elseby/SebyDBtnX/hardware/SebyDBtn4/pcb/4.0/PNG_Schematic_1_2025-09-06/SCH_Schematic_1_1-HIBus Interface - Power_2025-09-06.png

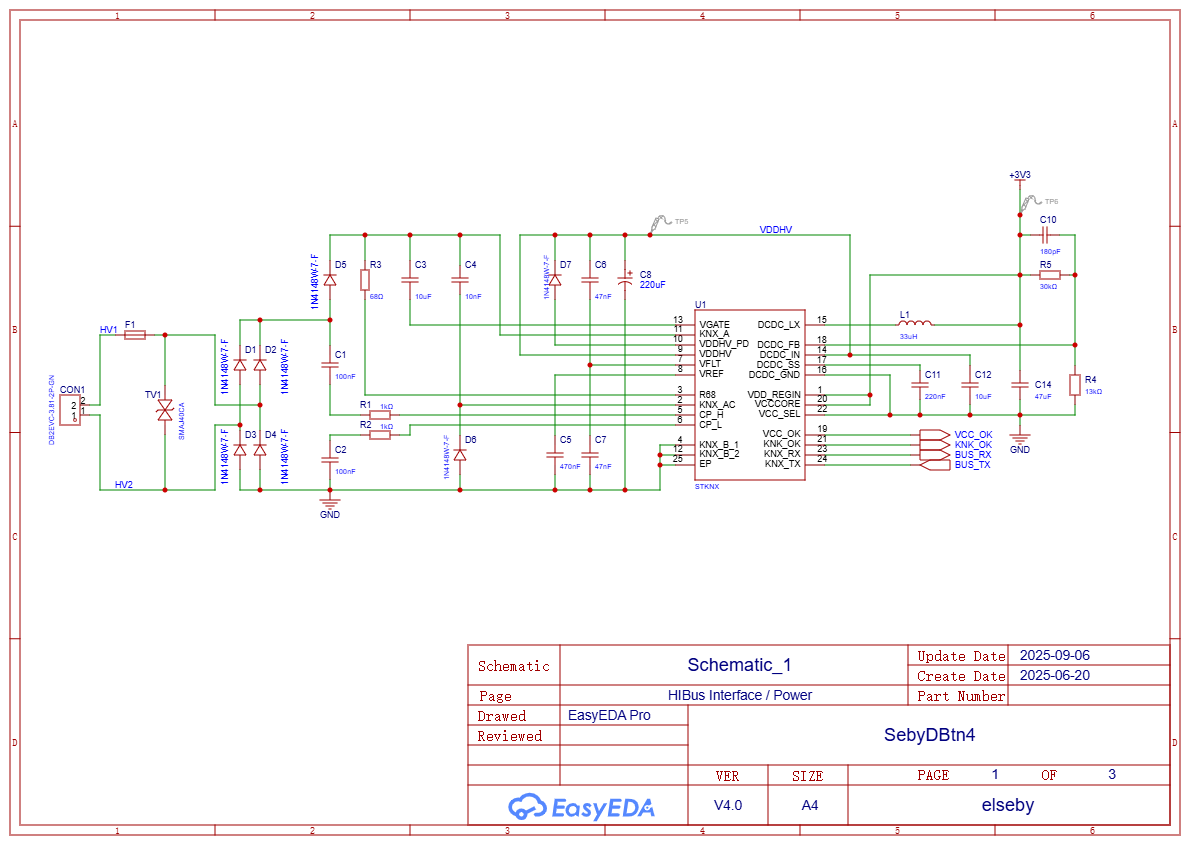
hardware/SebyDBtn4/pcb/4.0/PNG_Schematic_1_2025-09-06/SCH_Schematic_1_1-HIBus Interface - Power_2025-09-06.png
