elseby/SebyDBtnX/images/3D_SebyDBtn8_PCB_3.0_back.png

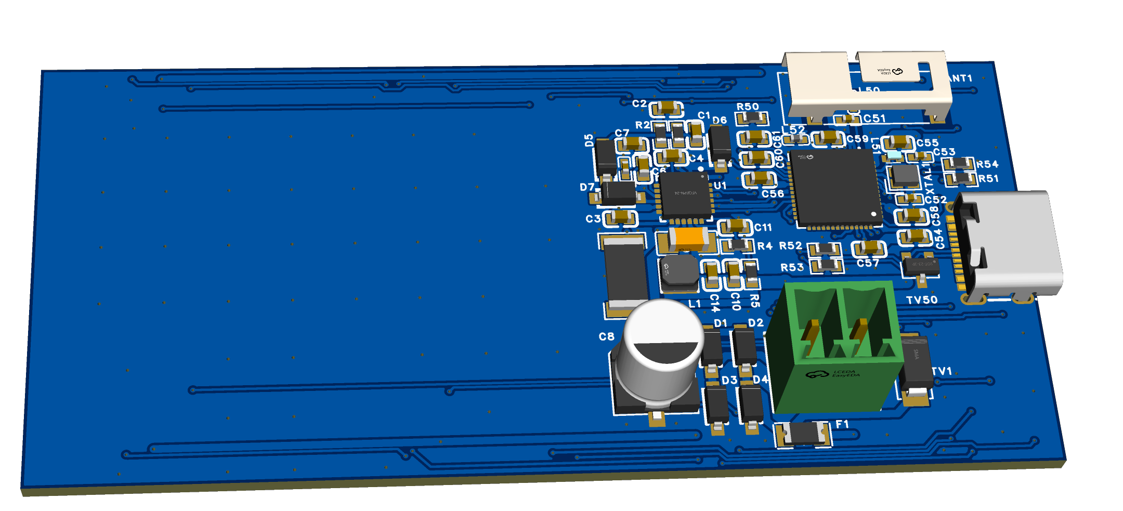
images/3D_SebyDBtn8_PCB_3.0_back.png
