elseby/SebyDBtnX/images/3D_SebyDBtn8_PCB_3.0_front.png

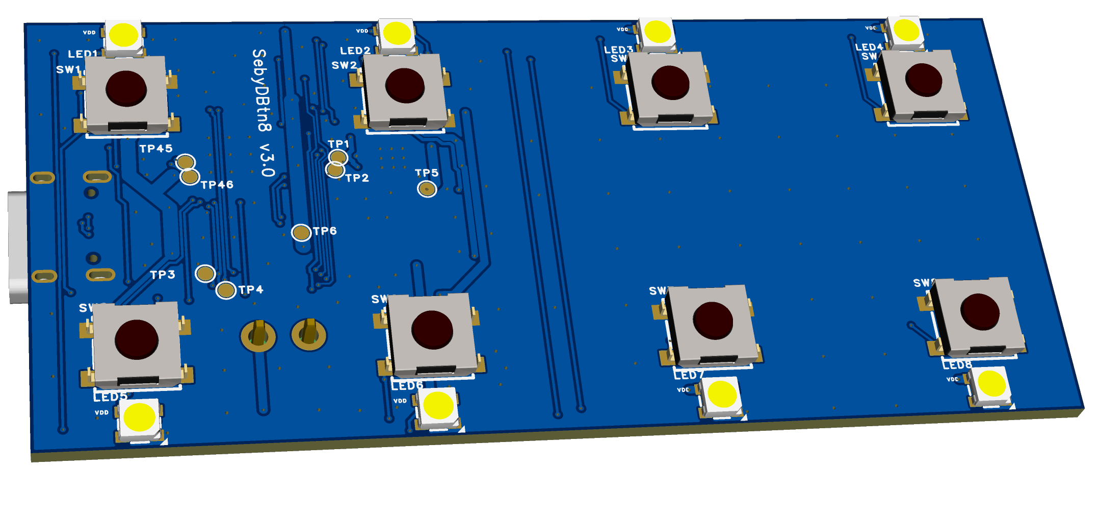
images/3D_SebyDBtn8_PCB_3.0_front.png
