elseby/SebyDBtnX/images/SebyDBtn4_coverfront.png

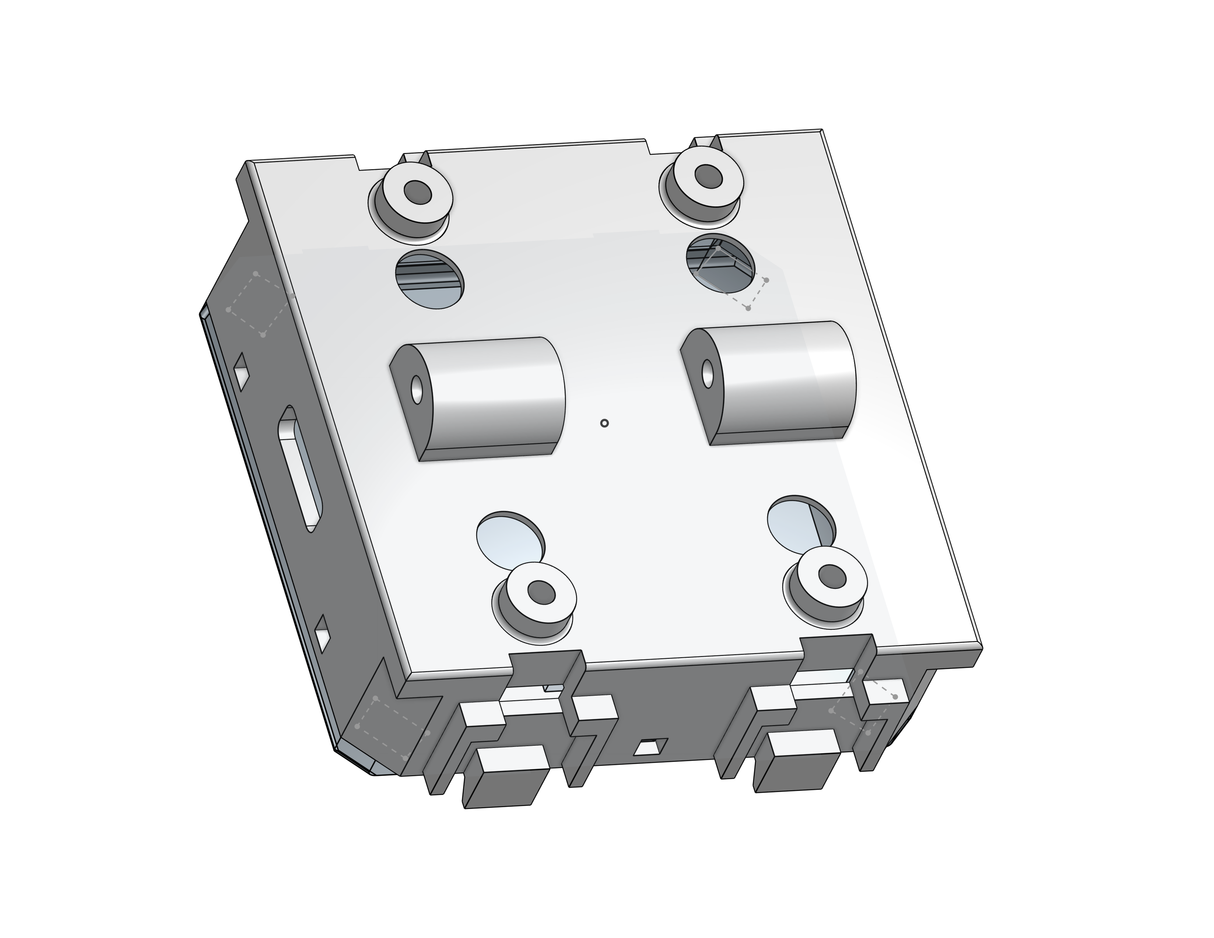
images/SebyDBtn4_coverfront.png
