elseby/SebyDBtnX/images/SebyDBtn8_BackCover_V3.0.png

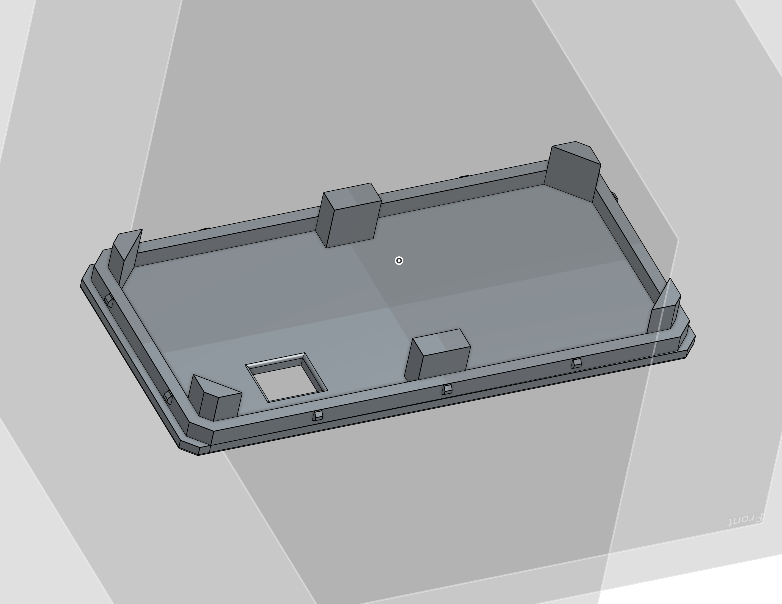
images/SebyDBtn8_BackCover_V3.0.png
