elseby/SebyDBtnX/images/SebyDBtn8_cover.png

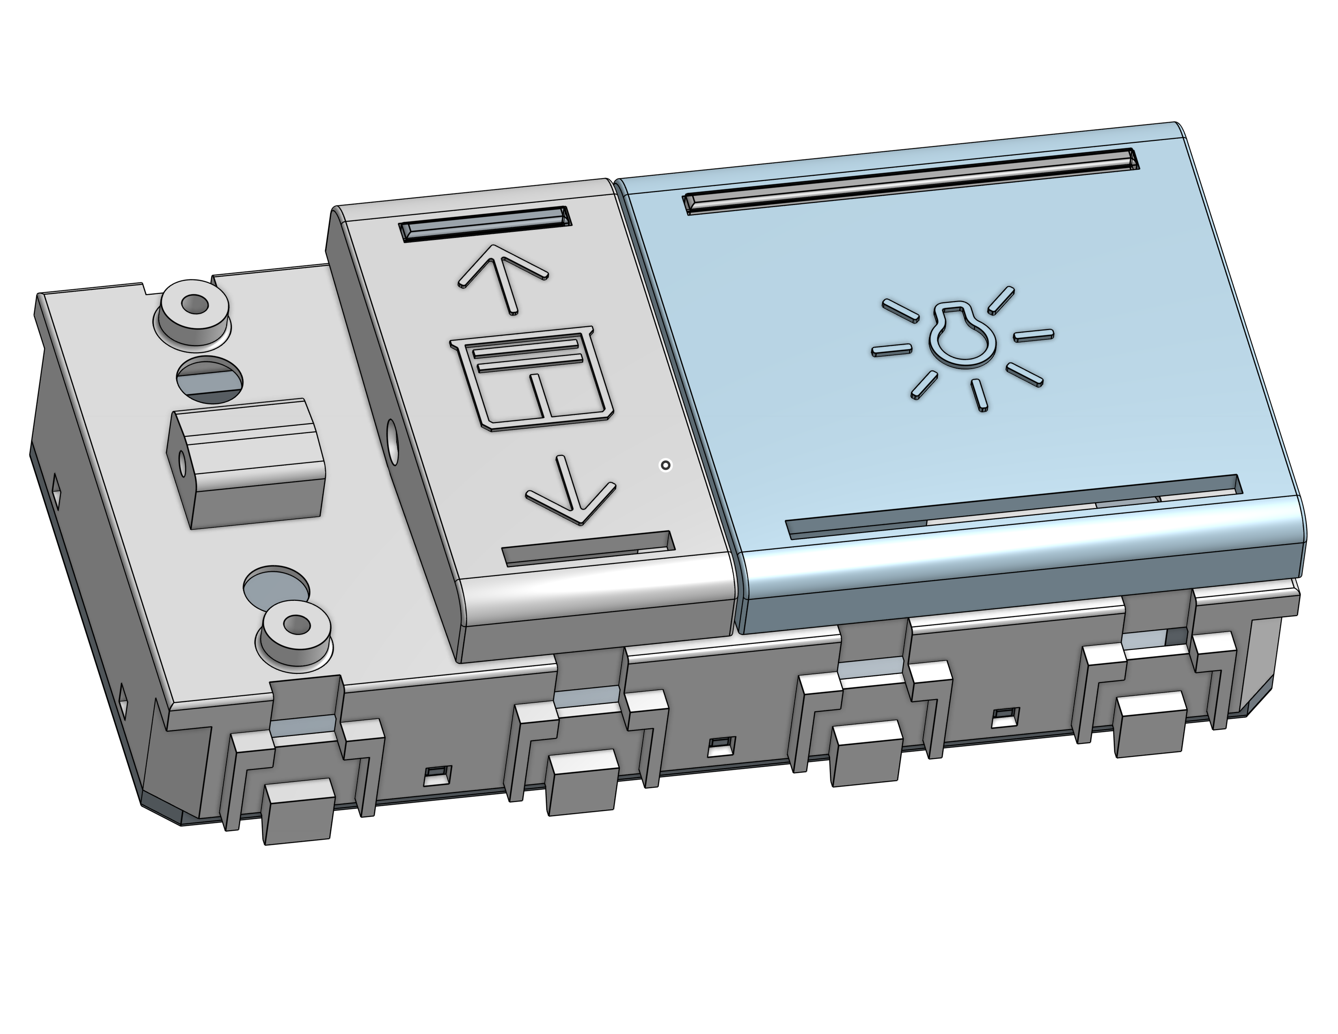
images/SebyDBtn8_cover.png
