elseby/SebyDBtnX/images/SebyDBtnx_Key_Cover_1pos_V3.0.png

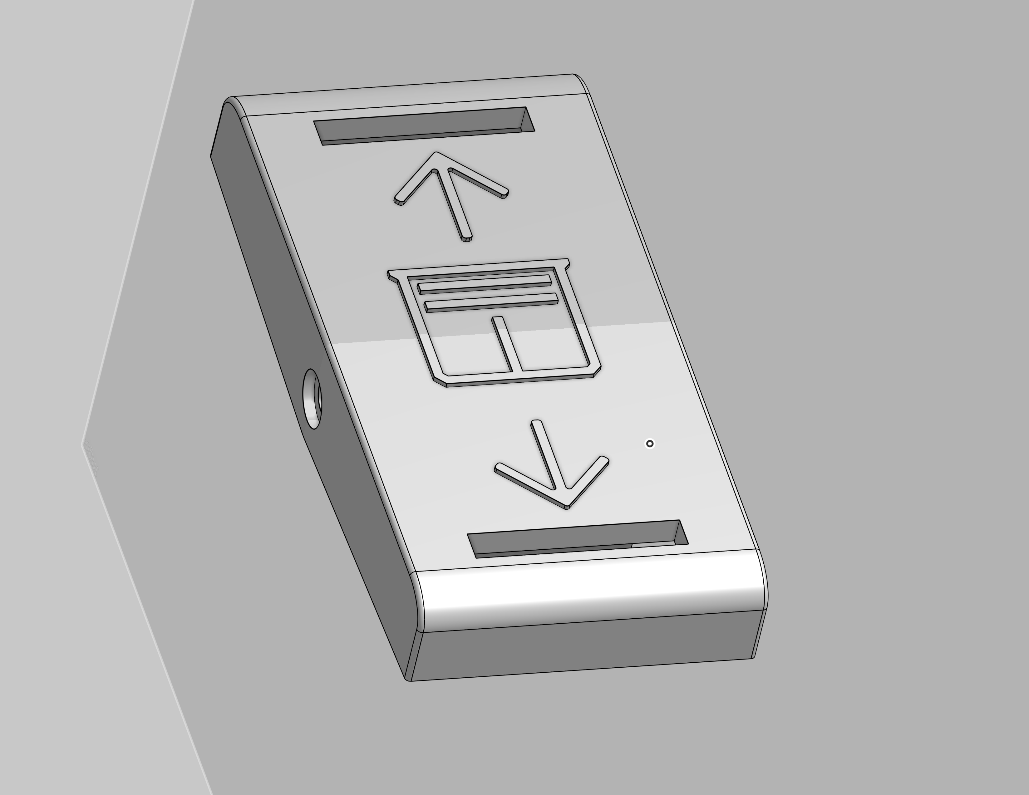
images/SebyDBtnx_Key_Cover_1pos_V3.0.png
