elseby/SebyDBtnX/images/SebyDBtnx_Key_Light_1pos_V3.0.png

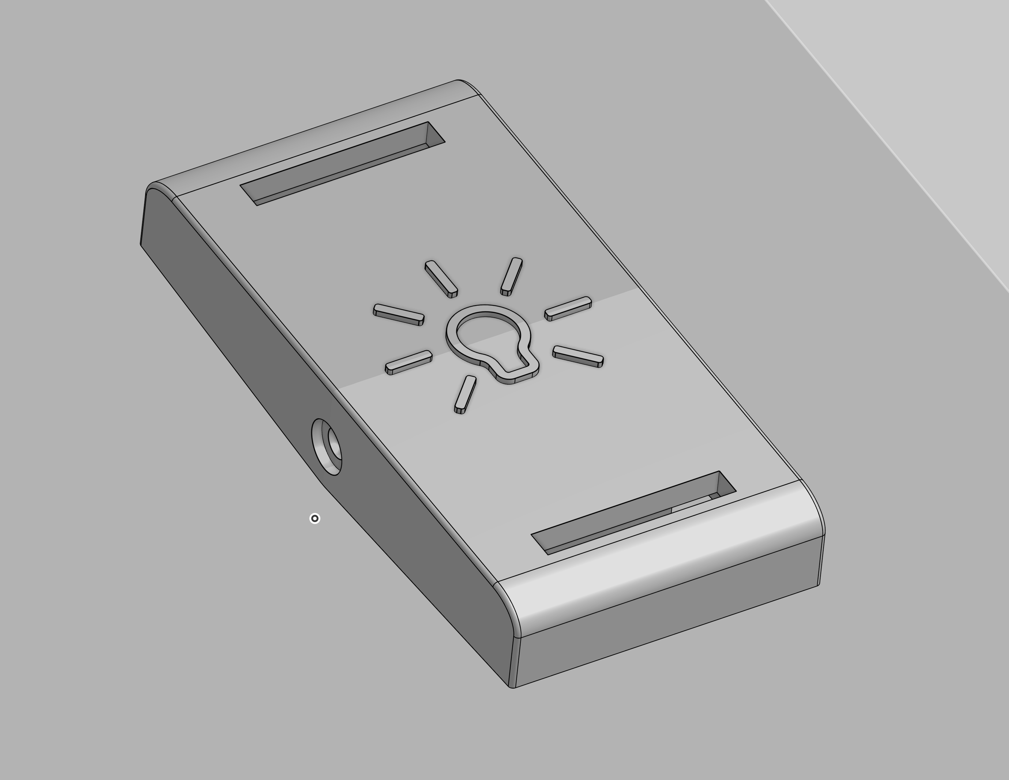
images/SebyDBtnx_Key_Light_1pos_V3.0.png
