elseby/SebyDBtnX/images/SebyDBtnx_Key_Light_2pos_V3.0.png

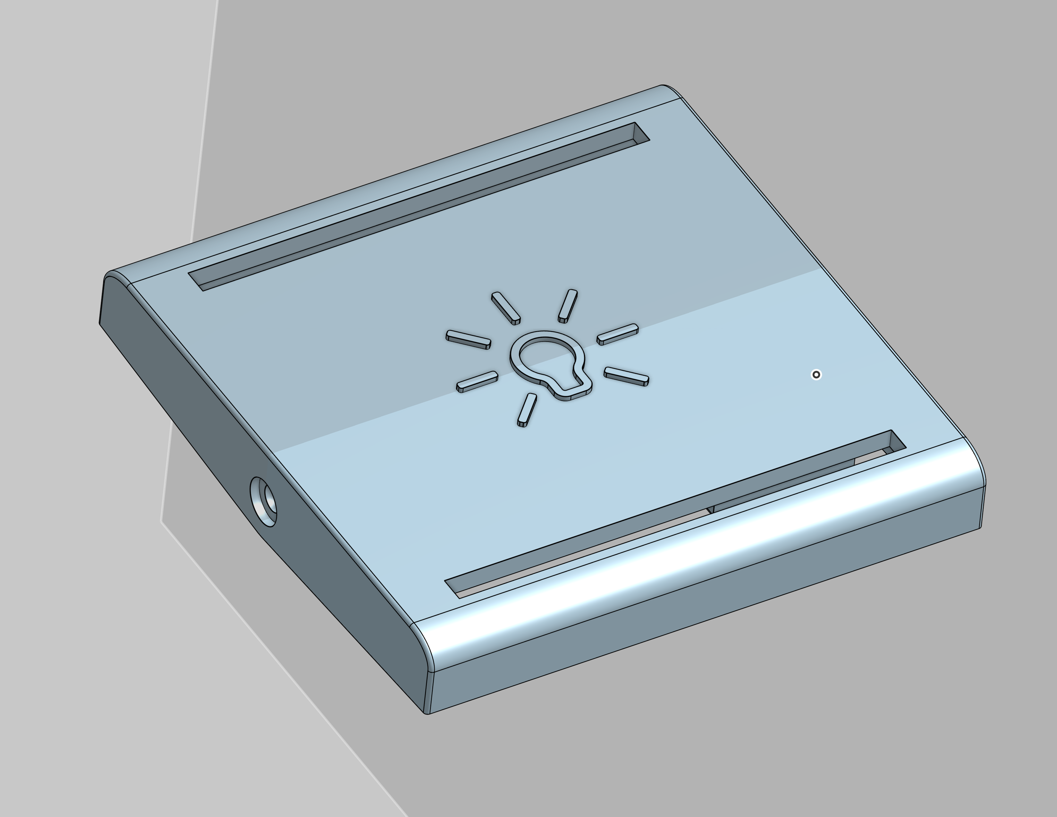
images/SebyDBtnx_Key_Light_2pos_V3.0.png
