elseby/SebyDBtnX/images/SebyDBtnx_LightGuide_1pos_V3.0.png

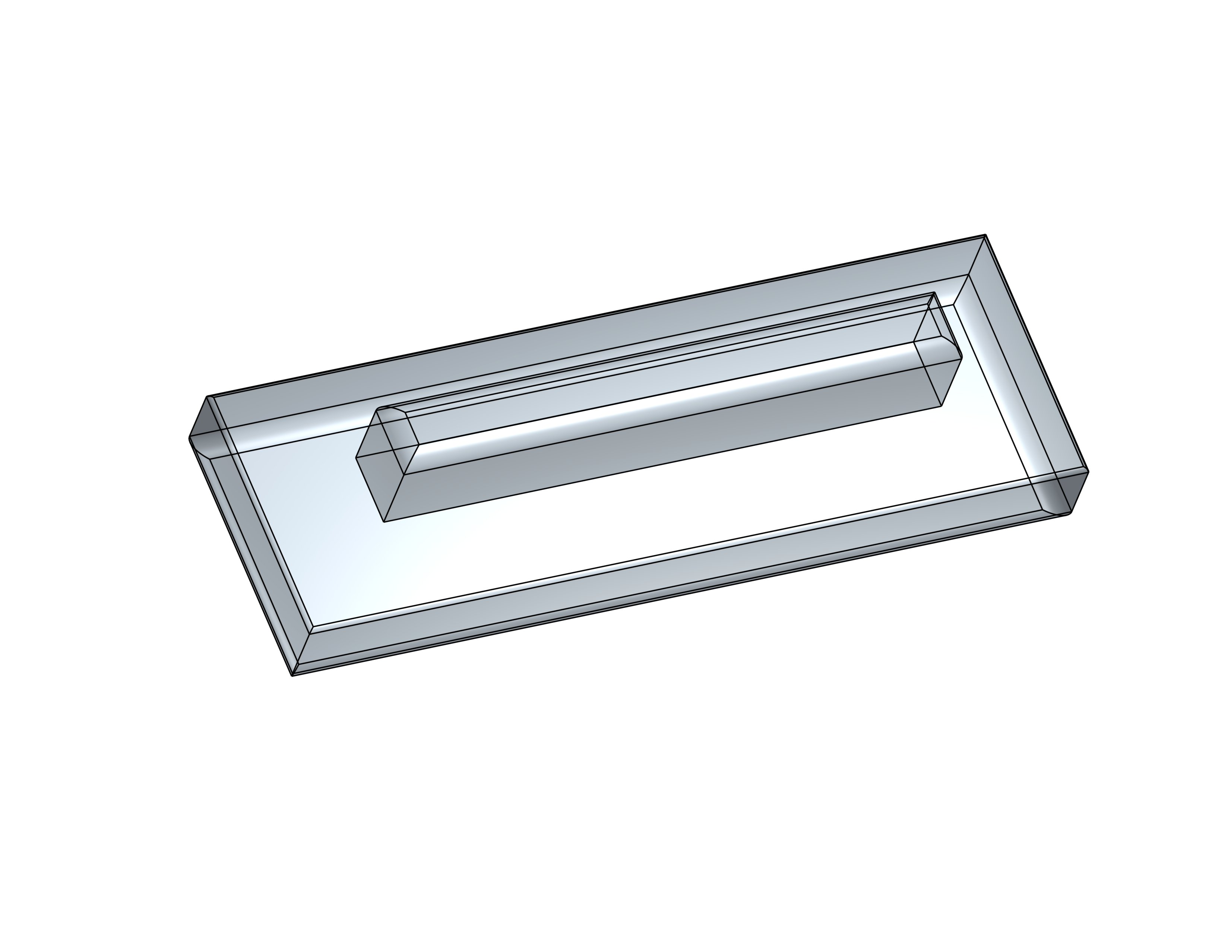
images/SebyDBtnx_LightGuide_1pos_V3.0.png
