elseby/SebyDBtnX/images/SebyDBtnx_LightGuide_2pos_V3.0.png

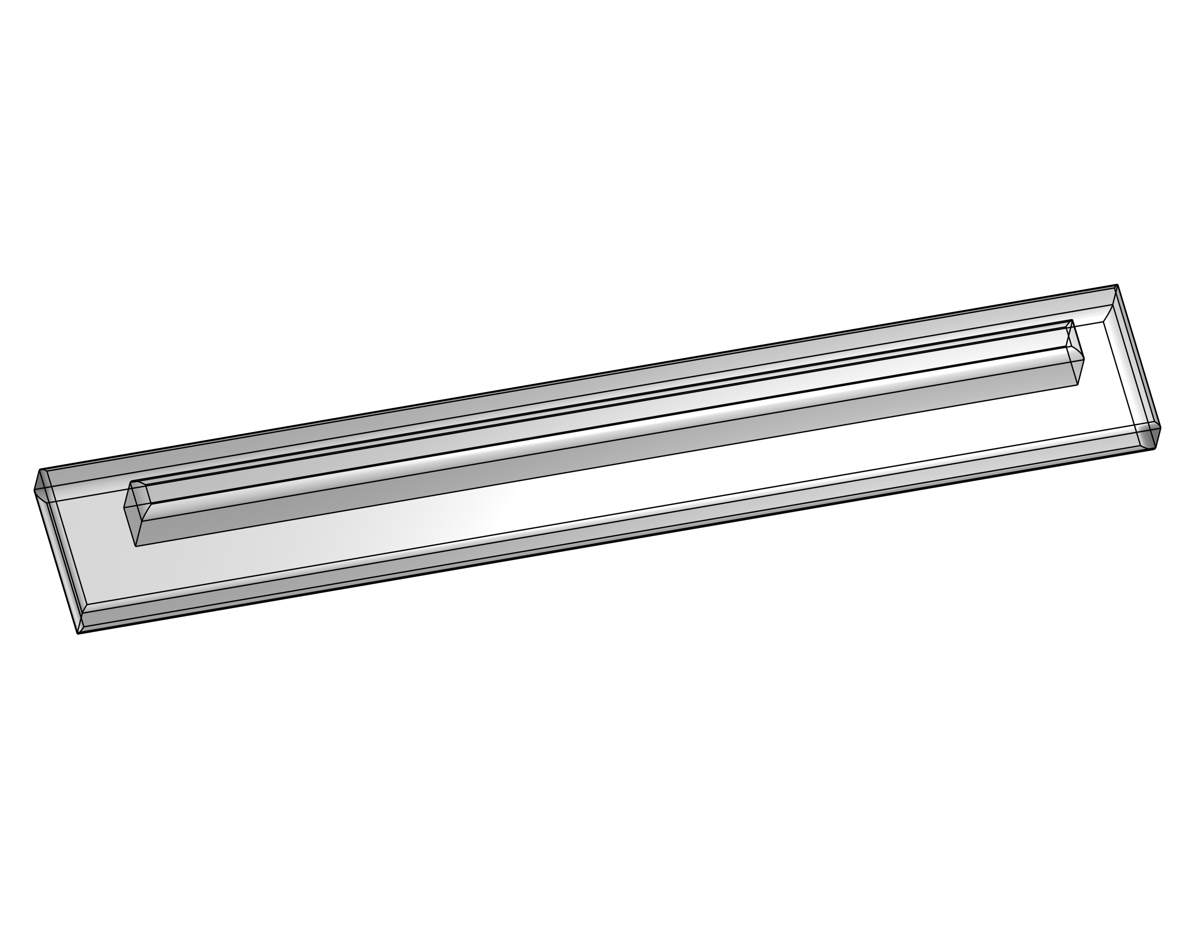
images/SebyDBtnx_LightGuide_2pos_V3.0.png
