elseby/SebyDBtnX/main/otaupload.c

/*
 * otaupload.c
 *
 *  Created on: 3 apr 2025
 *      Author: sebmar
 */
#include "include/otaupload.h"
#include <stdint.h>
#include <string.h>
#include <freertos/FreeRTOS.h>
#include <esp_http_server.h>
#include <freertos/task.h>
#include <esp_ota_ops.h>
#include <esp_system.h>
#include <nvs_flash.h>
#include <sys/param.h>
#include <esp_wifi.h>

/*
 * Serve OTA update portal (index.html)
 */
extern const uint8_t index_html_start[] asm("_binary_otaupload_html_start");
extern const uint8_t index_html_end[] asm("_binary_otaupload_html_end");

esp_err_t index_get_handler(httpd_req_t *req)
{
	httpd_resp_send(req, (const char *) index_html_start, index_html_end - index_html_start);
	return ESP_OK;
}

/*
 * Handle OTA file upload
 */
esp_err_t update_post_handler(httpd_req_t *req)
{
	char buf[1000];
	esp_ota_handle_t ota_handle;
	int remaining = req->content_len;

	const esp_partition_t *ota_partition = esp_ota_get_next_update_partition(NULL);
	ESP_ERROR_CHECK(esp_ota_begin(ota_partition, OTA_SIZE_UNKNOWN, &ota_handle));

	while (remaining > 0) {
		int recv_len = httpd_req_recv(req, buf, MIN(remaining, sizeof(buf)));

		// Timeout Error: Just retry
		if (recv_len == HTTPD_SOCK_ERR_TIMEOUT) {
			continue;

		// Serious Error: Abort OTA
		} else if (recv_len <= 0) {
			httpd_resp_send_err(req, HTTPD_500_INTERNAL_SERVER_ERROR, "Protocol Error");
			return ESP_FAIL;
		}

		// Successful Upload: Flash firmware chunk
		if (esp_ota_write(ota_handle, (const void *)buf, recv_len) != ESP_OK) {
			httpd_resp_send_err(req, HTTPD_500_INTERNAL_SERVER_ERROR, "Flash Error");
			return ESP_FAIL;
		}

		remaining -= recv_len;
	}

	// Validate and switch to new OTA image and reboot
	if (esp_ota_end(ota_handle) != ESP_OK || esp_ota_set_boot_partition(ota_partition) != ESP_OK) {
			httpd_resp_send_err(req, HTTPD_500_INTERNAL_SERVER_ERROR, "Validation / Activation Error");
			return ESP_FAIL;
	}

	httpd_resp_sendstr(req, "Firmware update complete, rebooting now!<br><a href=\"/\">reload</a>");

	vTaskDelay(500 / portTICK_PERIOD_MS);
	esp_restart();

	return ESP_OK;
}

/*
 * HTTP Server
 */
httpd_uri_t index_get = {
	.uri	  = "/update",
	.method   = HTTP_GET,
	.handler  = index_get_handler,
	.user_ctx = NULL
};

httpd_uri_t update_post = {
	.uri	  = "/update",
	.method   = HTTP_POST,
	.handler  = update_post_handler,
	.user_ctx = NULL
};

void otaInit(httpd_handle_t http_server, httpd_config_t config) {
	esp_err_t ret = nvs_flash_init();

	if (ret == ESP_ERR_NVS_NO_FREE_PAGES || ret == ESP_ERR_NVS_NEW_VERSION_FOUND) {
		ESP_ERROR_CHECK(nvs_flash_erase());
		ret = nvs_flash_init();
	}

	ESP_ERROR_CHECK(ret);
//	ESP_ERROR_CHECK(softap_init());
//	ESP_ERROR_CHECK(http_server_init());

	httpd_register_uri_handler(http_server, &index_get);
	httpd_register_uri_handler(http_server, &update_post);

	/* Mark current app as valid */
	const esp_partition_t *partition = esp_ota_get_running_partition();
	printf("Currently running partition: %s\r\n", partition->label);

	esp_ota_img_states_t ota_state;
	if (esp_ota_get_state_partition(partition, &ota_state) == ESP_OK) {
		if (ota_state == ESP_OTA_IMG_PENDING_VERIFY) {
			esp_ota_mark_app_valid_cancel_rollback();
		}
	}

}
